FLRHW/Isolated_12to450V/HTML/images/cat_pdf_drill_map_Isolated_12to450V-PTH_drill_map.png

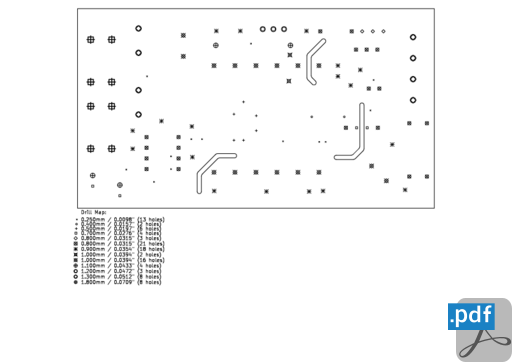
HTML/images/cat_pdf_drill_map_Isolated_12to450V-PTH_drill_map.png
