FLRHW/Isolated_12to450V/HTML/images/cat_png_3d_viewer_bottom_Isolated_12to450V-bottom.png

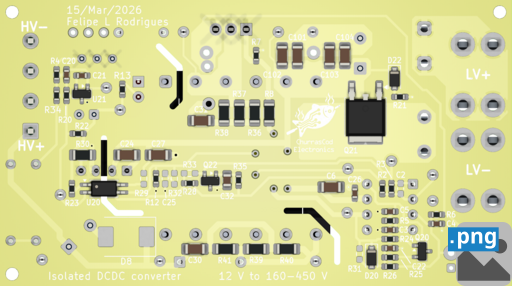
HTML/images/cat_png_3d_viewer_bottom_Isolated_12to450V-bottom.png
