FLRHW/Isolated_12to450V/HTML/images/cat_png_3d_viewer_top_Isolated_12to450V-top.png

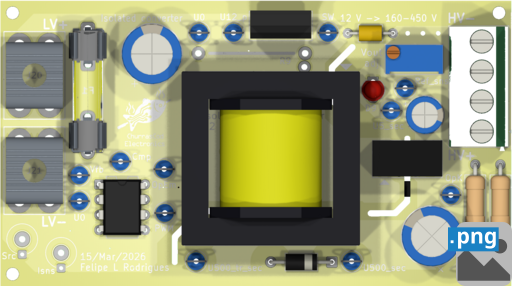
HTML/images/cat_png_3d_viewer_top_Isolated_12to450V-top.png
