FLRHW/Isolated_12to450V/Manufacturing/Fabrication/Gerbers/Isolated_12to450V-F_Silkscreen.pdf

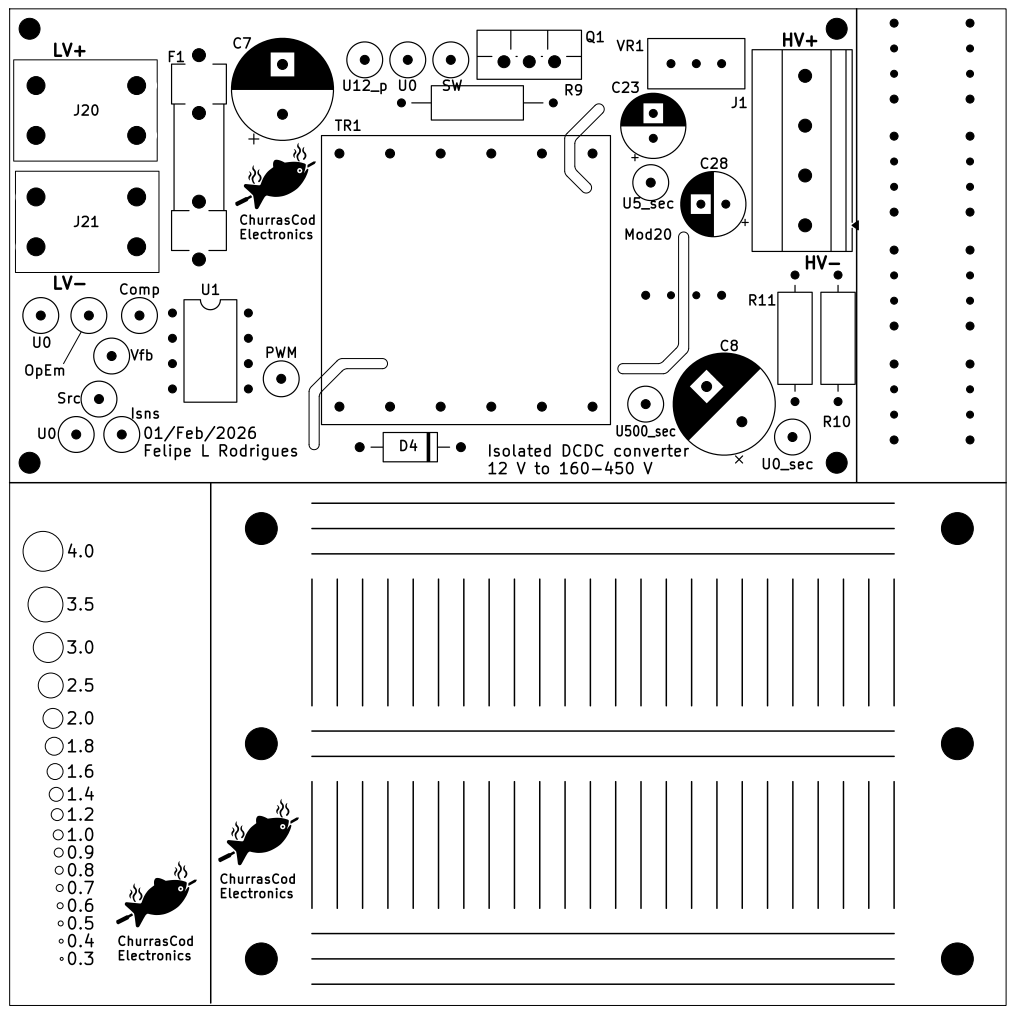
[picture p38: page 1]
