FLRHW/Isolated_12to450V/Manufacturing/Fabrication/Gerbers/Isolated_12to450V-L1 (Ref).pdf

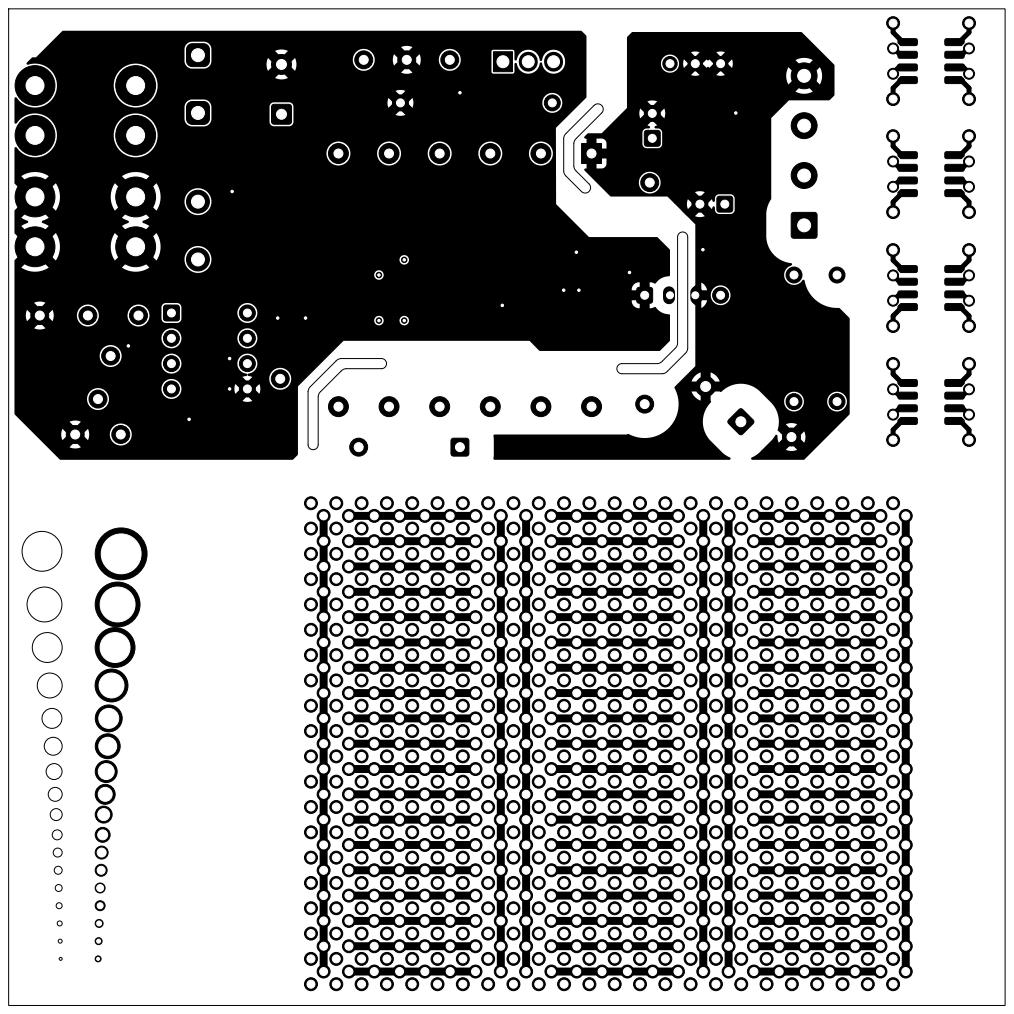
[picture p39: page 1]
