FLRHW/Isolated_12to450V/Manufacturing/Fabrication/Gerbers/Isolated_12to450V-L2 (Sig, PWR).pdf

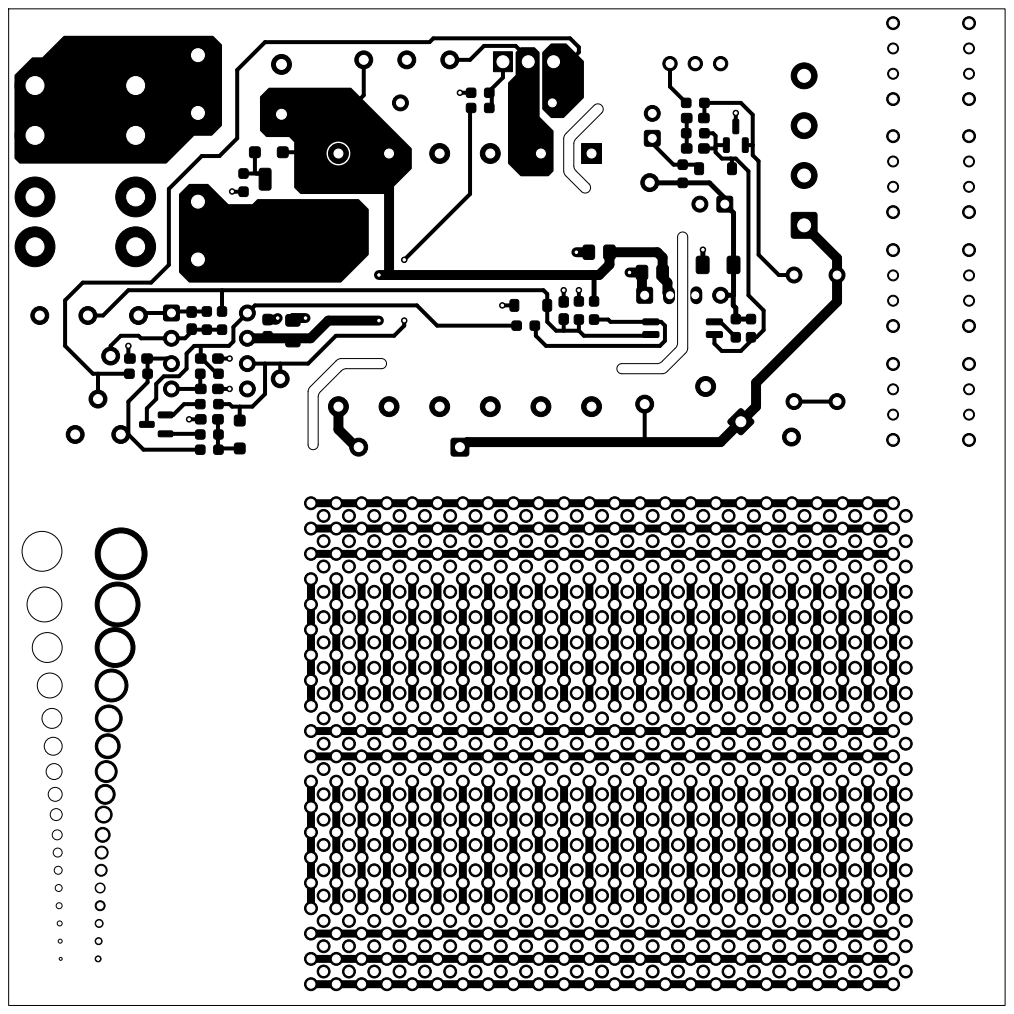
[picture p40: page 1]
