FLRHW/Isolated_12to450V/Manufacturing/Fabrication/Gerbers/Isolated_12to450V-Virtual (Bot side jumpers).pdf

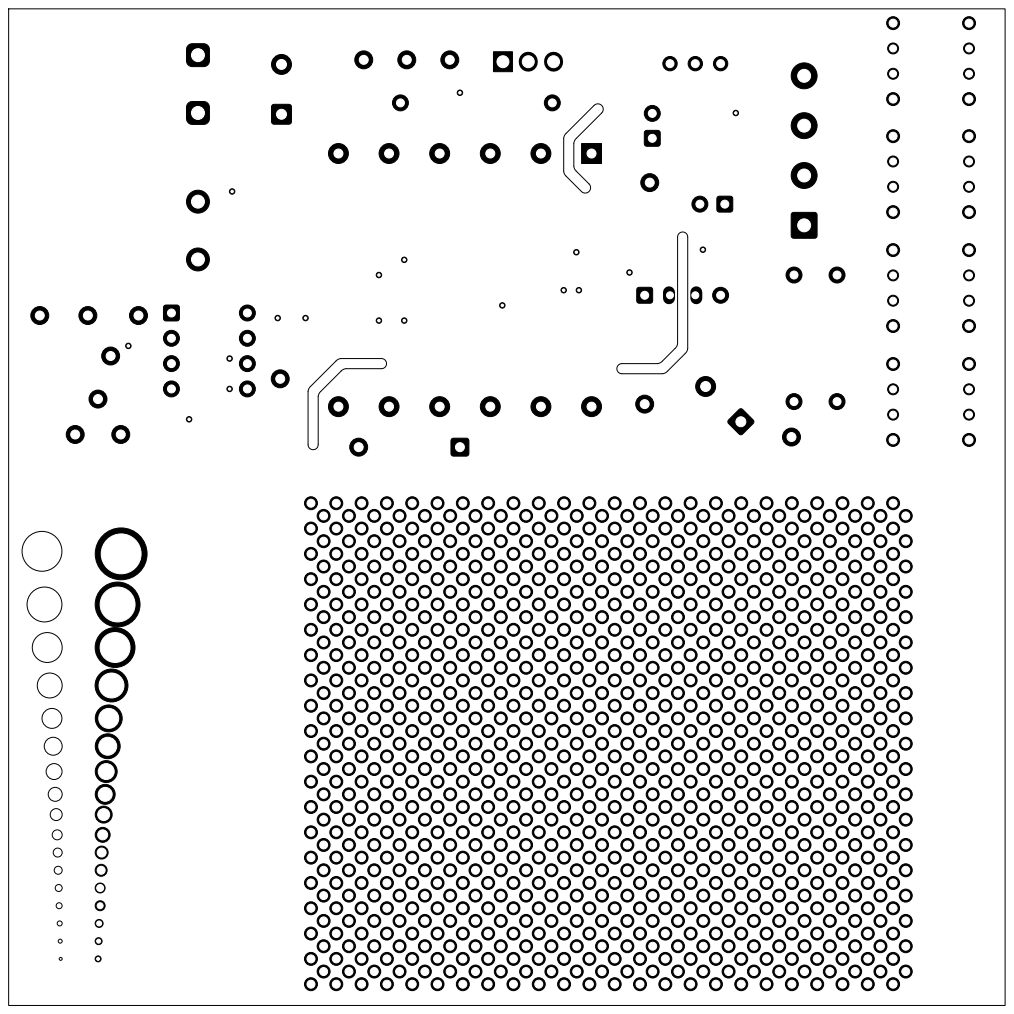
[picture p41: page 1]
