FLRHW/Isolated_12to450V/Manufacturing/Fabrication/Gerbers/Isolated_12to450V-Virtual (Top side jumpers).pdf

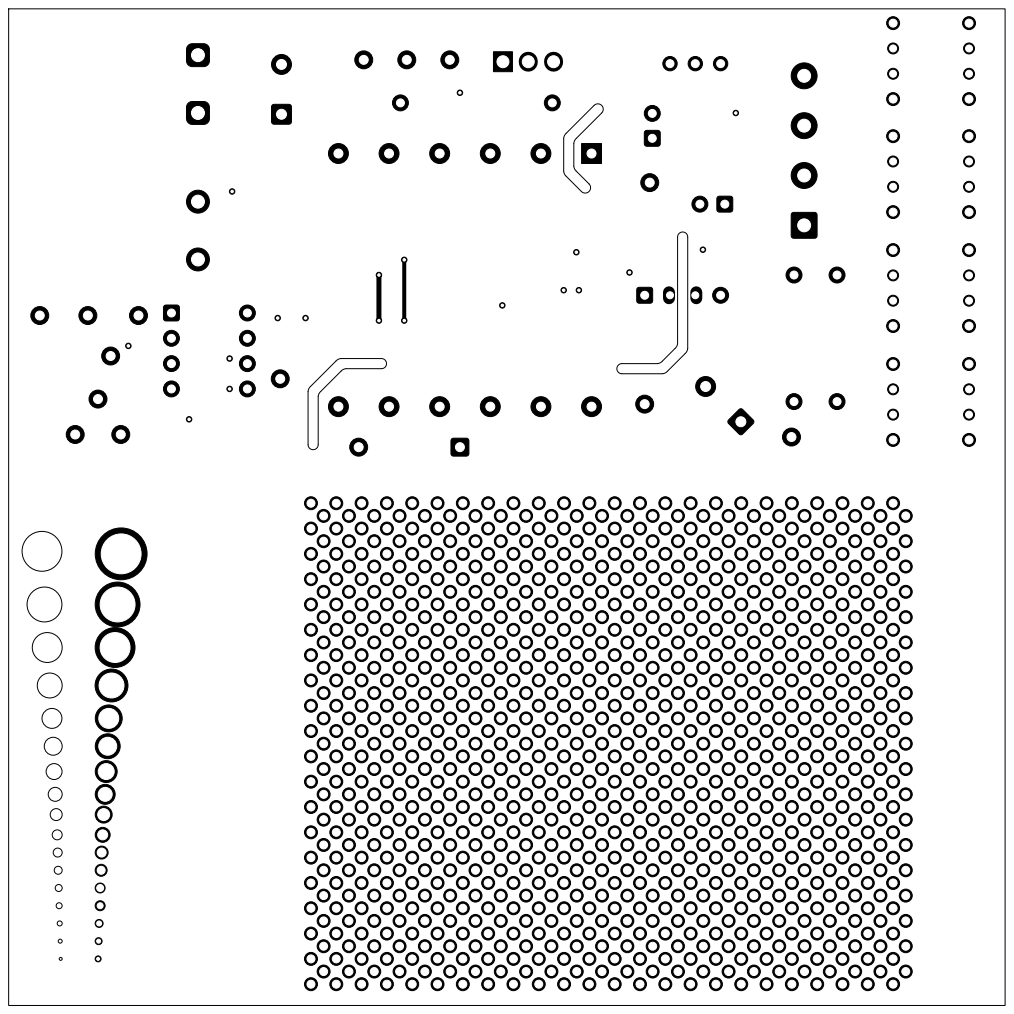
[picture p42: page 1]
